Sola85/spdif-volume-control/schematic/toslink-volume-control.kicad_sch

## KiCad design schematic/toslink-volume-control.kicad_sch (2025-05-17)

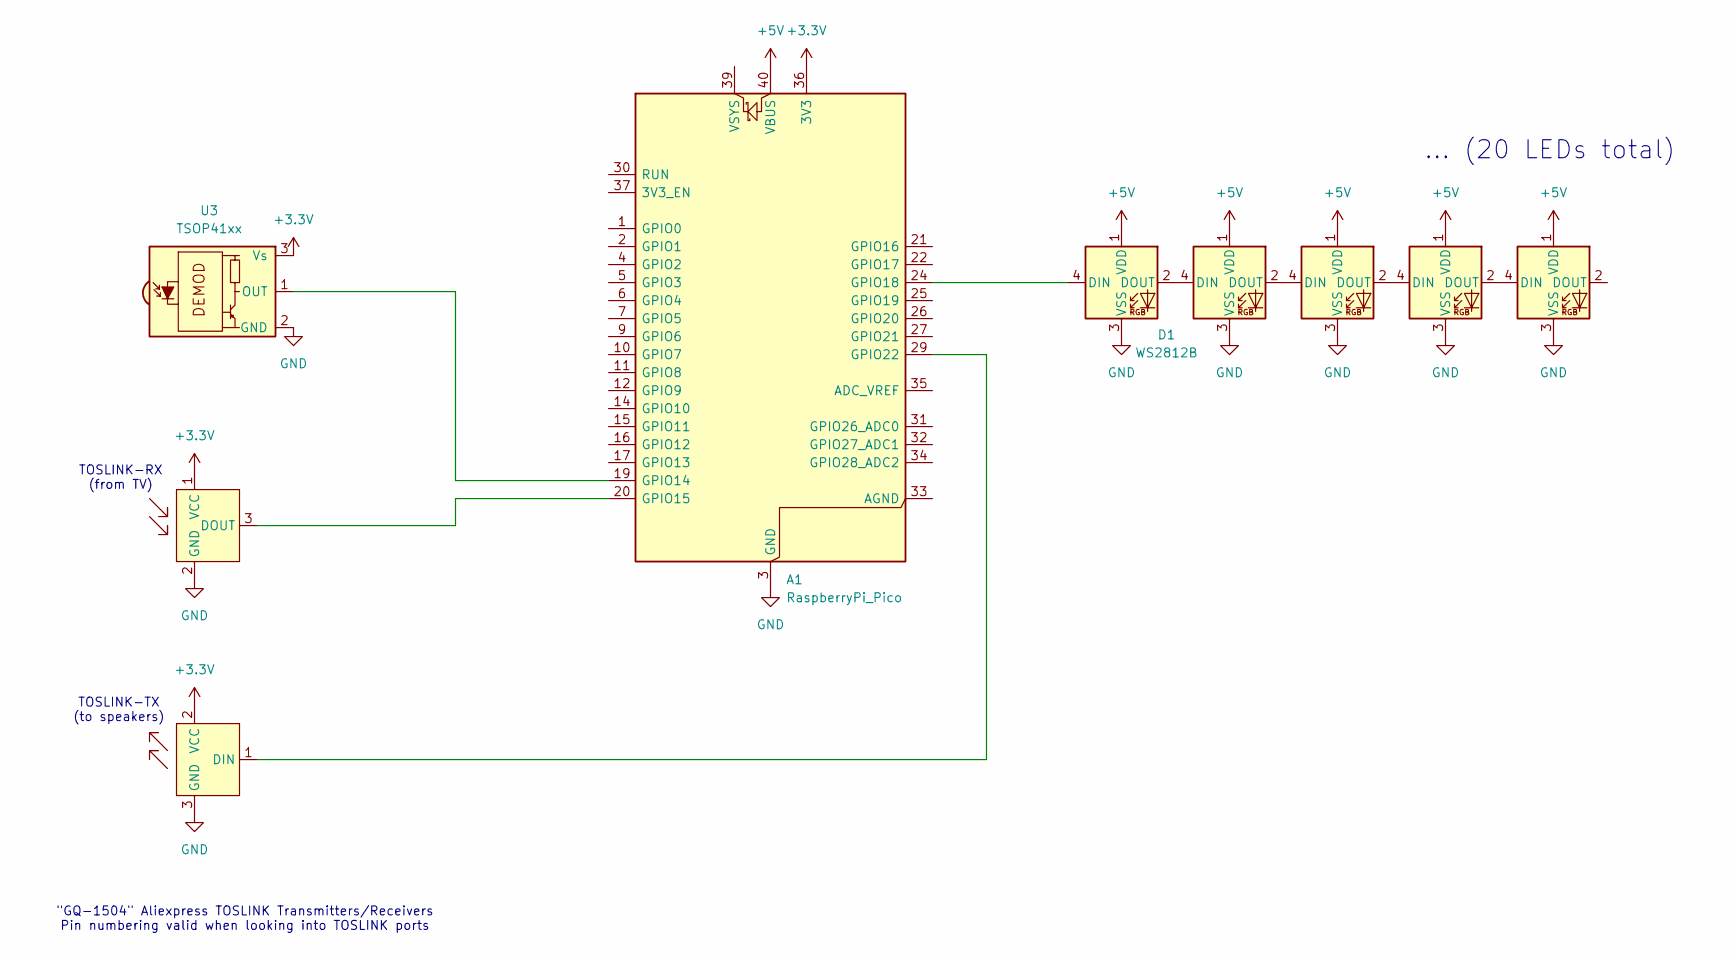
[picture p3: schematic toslink-volume-control.kicad_sch]

Parts:
A1: RaspberryPi_Pico; RaspberryPi_Pico_Common_Unspecified
D1, D2, D3, D4, D5: WS2812B; LED_WS2812B_PLCC4_5.0x5.0mm_P3.2mm
U1, U2: (no value)
U3: TSOP41xx; Vishay_MOLD-3Pin

Connections:
+3.3V: A1.36 (3V3), U1.1 (VCC), U2.2 (VCC), U3.3 (Vs)
+5V: A1.40 (VBUS), D1.1 (VDD), D2.1 (VDD), D3.1 (VDD), D4.1 (VDD), D5.1 (VDD)
GND: A1.3 (GND), A1.8 (GND), A1.13 (GND), A1.18 (GND), A1.23 (GND), A1.28 (GND), A1.38 (GND), D1.3 (VSS), D2.3 (VSS), D3.3 (VSS), D4.3 (VSS), D5.3 (VSS), U1.2 (GND), U2.3 (GND), U3.2 (GND)
unnamed: A1.19 (GPIO14), U3.1 (OUT)
unnamed: A1.20 (GPIO15), U1.3 (DOUT)
unnamed: A1.24 (GPIO18), D1.4 (DIN)
unnamed: A1.29 (GPIO22), U2.1 (DIN)
unnamed: D1.2 (DOUT), D2.4 (DIN)
unnamed: D2.2 (DOUT), D3.4 (DIN)
unnamed: D3.2 (DOUT), D4.4 (DIN)
unnamed: D4.2 (DOUT), D5.4 (DIN)

Notes on the sheet:
TOSLINK-TX (to speakers)
"GQ-1504" Aliexpress TOSLINK Transmitters/Receivers Pin numbering valid when looking into TOSLINK ports
... (20 LEDs total)
TOSLINK-RX (from TV)
